jrg-tools/inkbridge/src/homeassistant/HomeAssistantClient.cpp

#include "HomeAssistantClient.h"

#include <ArduinoJson.h>
#include <HTTPClient.h>

void HomeAssistantClient::begin(const String& host, int port, const String& token) {
  // Accept a bare host ("homeassistant.local") or one already carrying a
  // scheme ("https://..."), so a user pasting a full URL doesn't produce a
  // double-scheme "http://https://..." — which HTTPClient parses as host
  // "https" and fails DNS.
  String scheme = "http://";
  String bareHost = host;
  if (bareHost.startsWith("https://")) {
    scheme = "https://";
    bareHost.remove(0, 8);
  } else if (bareHost.startsWith("http://")) {
    bareHost.remove(0, 7);
  }
  // port <= 0 means "use the scheme's default port" (443/80) — e.g. a
  // reverse-proxied HTTPS install with no separate port to speak of.
  baseUrl = scheme + bareHost;
  if (port > 0) baseUrl += String(":") + port;
  authHeader = String("Bearer ") + token;
}

bool HomeAssistantClient::runScript(const String& scriptObjectId) {
  HTTPClient http;
  http.setTimeout(3000);
  http.begin(baseUrl + "/api/services/script/turn_on");
  http.addHeader("Authorization", authHeader);
  http.addHeader("Content-Type", "application/json");

  String entityId = "script." + scriptObjectId;
  int code = http.POST(String("{\"entity_id\":\"") + entityId + "\"}");
  http.end();
  Serial.printf("[HA] run %s -> %d\n", entityId.c_str(), code);
  return code == 200 || code == 201;
}

bool HomeAssistantClient::getTodoItems(const String& entityId, std::vector<TodoItem>& outItems) {
  HTTPClient http;
  http.setTimeout(5000);  // list fetch, not fire-and-forget — a bit more slack than runScript
  http.begin(baseUrl + "/api/services/todo/get_items?return_response=true");
  http.addHeader("Authorization", authHeader);
  http.addHeader("Content-Type", "application/json");

  int code = http.POST(String("{\"entity_id\":\"") + entityId + "\"}");
  if (code != 200 && code != 201) {
    Serial.printf("[HA] get_items %s -> %d\n", entityId.c_str(), code);
    http.end();
    return false;
  }
  String body = http.getString();
  http.end();

  JsonDocument doc;
  if (deserializeJson(doc, body) != DeserializationError::Ok) {
    Serial.println("[HA] get_items: invalid JSON response");
    return false;
  }
  JsonArrayConst items = doc["service_response"][entityId.c_str()]["items"].as<JsonArrayConst>();
  if (items.isNull()) {
    Serial.println("[HA] get_items: no service_response items for entity");
    return false;
  }
  for (JsonObjectConst entry : items) {
    TodoItem item;
    item.uid = entry["uid"] | "";
    item.text = entry["summary"] | "";
    item.checked = String((const char*)(entry["status"] | "")) == "completed";
    if (item.uid.length()) outItems.push_back(item);
  }
  return true;
}

bool HomeAssistantClient::updateTodoItem(const String& entityId, const String& uid, bool checked) {
  HTTPClient http;
  http.setTimeout(3000);
  http.begin(baseUrl + "/api/services/todo/update_item");
  http.addHeader("Authorization", authHeader);
  http.addHeader("Content-Type", "application/json");

  String status = checked ? "completed" : "needs_action";
  String payload = String("{\"entity_id\":\"") + entityId + "\",\"item\":\"" + uid +
                    "\",\"status\":\"" + status + "\"}";
  int code = http.POST(payload);
  http.end();
  Serial.printf("[HA] update_item %s (%s) -> %d\n", uid.c_str(), status.c_str(), code);
  return code == 200 || code == 201;
}

bool HomeAssistantClient::listTodoEntities(std::vector<TodoListInfo>& outLists) {
  // Built with map/zip/dict only — no `list.append()`/similar mutation.
  // HA's Jinja environment is sandboxed and rejects calling mutating methods
  // (a prior version of this used `{% set _ = result.append(...) %}`, which
  // renders fine in plain Jinja2 but gets a 400 from HA specifically because
  // of that sandboxing). `dict(zip(keys, values))` builds the {id: name}
  // mapping with only pure, always-permitted operations — a pattern
  // documented in HA's own templating docs. `s.name` is the state's
  // frontend display name (falls back to the entity id if unset).
  static const char* TEMPLATE =
      "{{ dict(zip(states.todo | map(attribute='entity_id') | list, "
      "states.todo | map(attribute='name') | list)) | tojson }}";

  JsonDocument reqDoc;
  reqDoc["template"] = TEMPLATE;
  String payload;
  serializeJson(reqDoc, payload);

  HTTPClient http;
  http.setTimeout(5000);
  http.begin(baseUrl + "/api/template");
  http.addHeader("Authorization", authHeader);
  http.addHeader("Content-Type", "application/json");

  int code = http.POST(payload);
  String body = http.getString();
  http.end();
  if (code != 200) {
    Serial.printf("[HA] template -> %d: %s\n", code, body.c_str());
    return false;
  }

  JsonDocument doc;
  if (deserializeJson(doc, body) != DeserializationError::Ok) {
    Serial.println("[HA] template: invalid JSON response");
    return false;
  }
  for (JsonPairConst kv : doc.as<JsonObjectConst>()) {
    TodoListInfo info;
    info.entityId = kv.key().c_str();
    info.name = kv.value() | "";
    if (info.entityId.length()) outLists.push_back(info);
  }
  return true;
}
